tadenham/OpenAWS/cad/WindDirectionHousing.stp

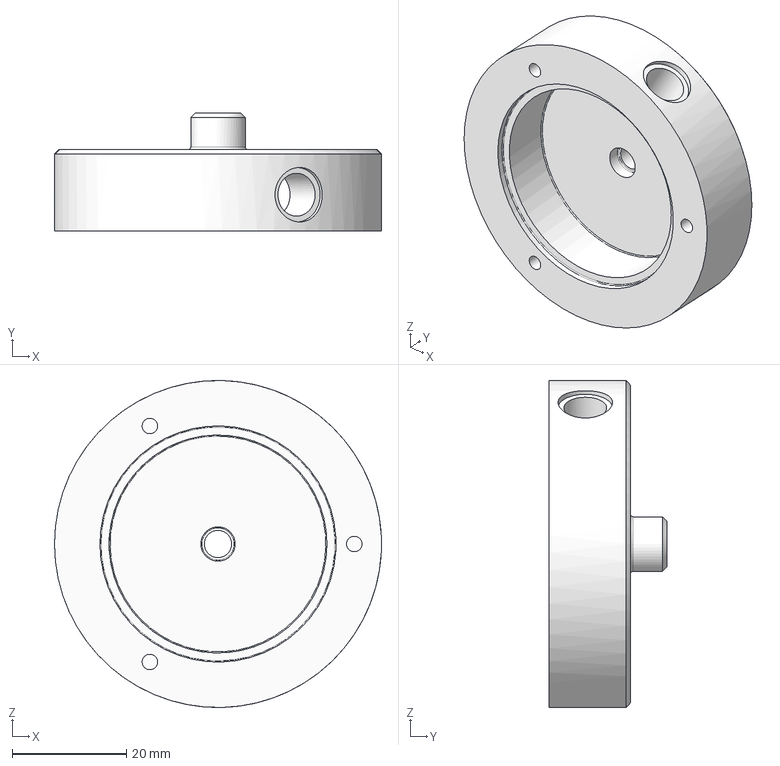
[picture p16: CAD file, 2026-05-12]
cad/WindDirectionHousing.stp
57.1 x 20.6 x 57.1 mm
