tadenham/OpenAWS/cad/WindSpeedHousing.stp

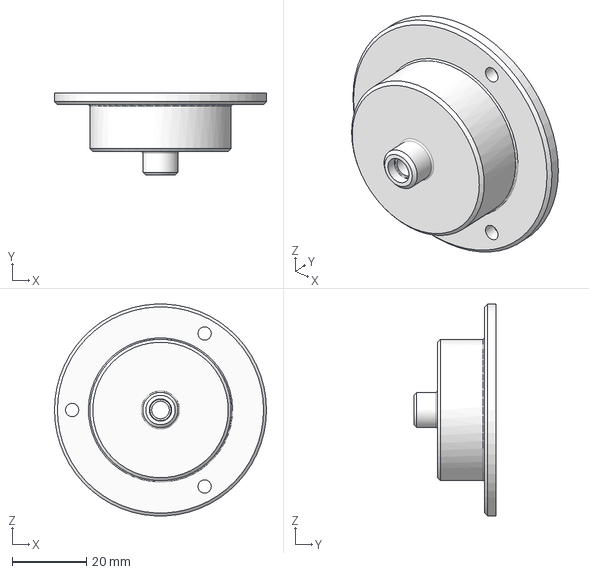
[picture p17: CAD file, 2026-05-12]
cad/WindSpeedHousing.stp
57.1 x 22.2 x 57.1 mm
